valerietsoi/4x3_derived/example/keyboard-layout.png

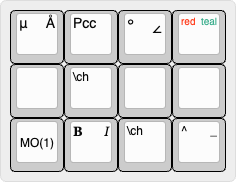
example/keyboard-layout.png
