valerietsoi/4x3_derived/images/render1.png

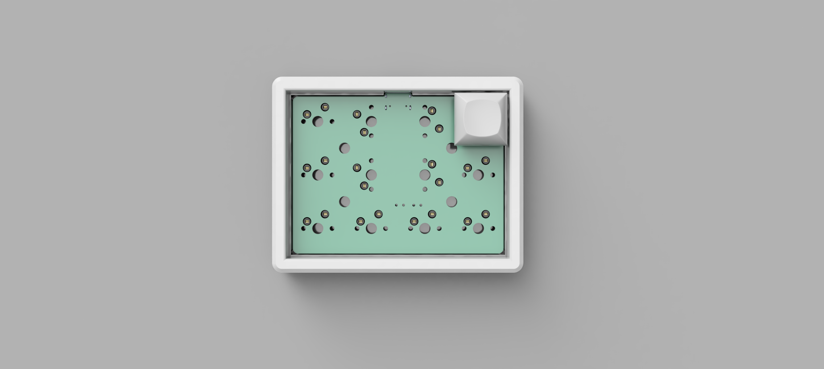
images/render1.png
