valerietsoi/4x3_derived/renders/Screenshot 2026-02-11 at 15.05.23.png

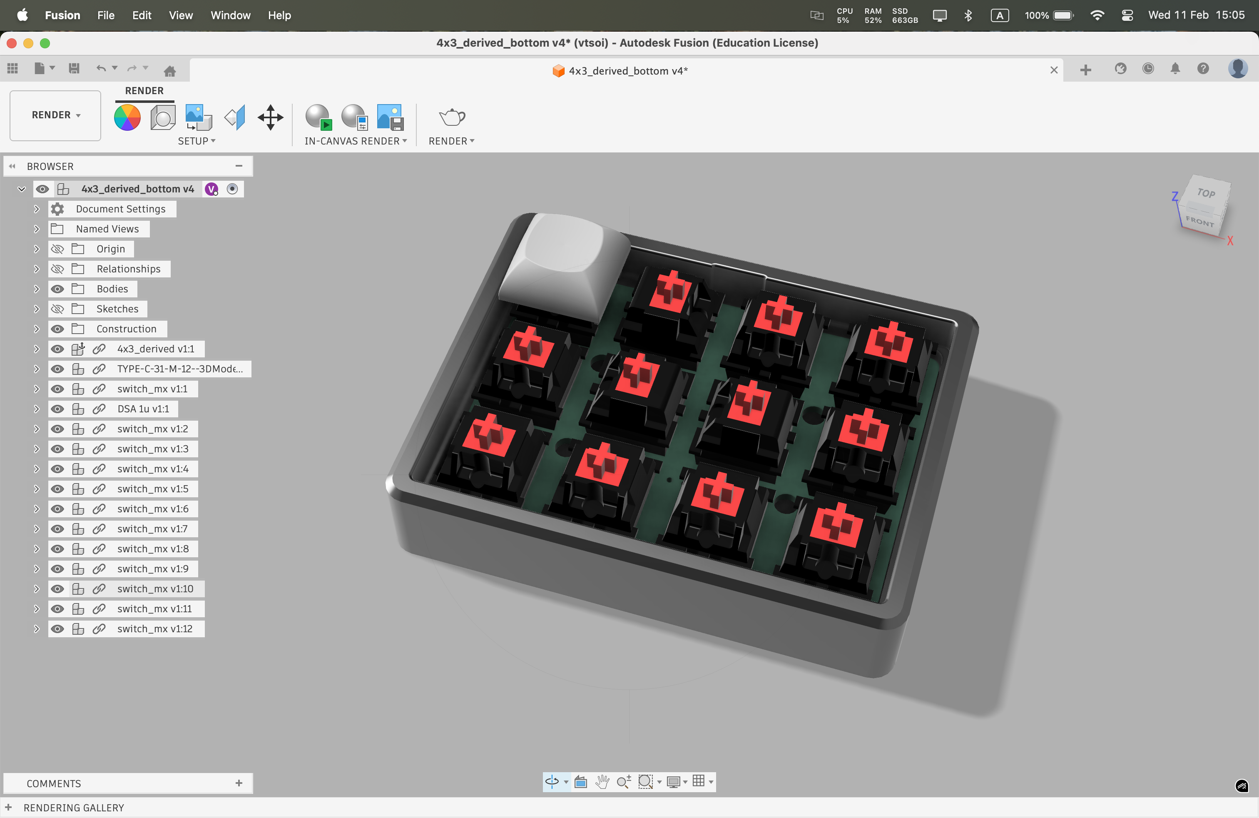
renders/Screenshot 2026-02-11 at 15.05.23.png
