valerietsoi/4x3_derived/images/_DSC4865.JPG

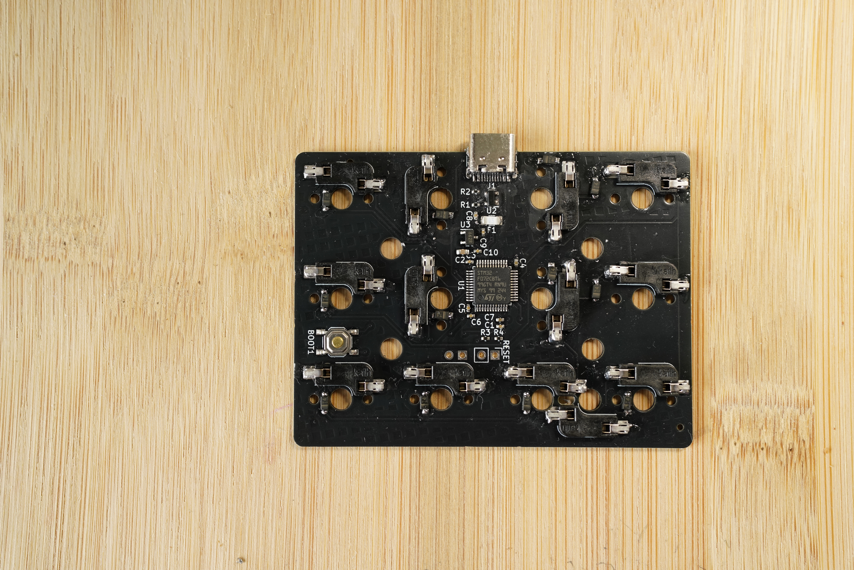
images/_DSC4865.JPG
